BoujeeEnjinia1701/leaklisten/cad/drawings/LKL-DWG-001.pdf

CONCEPT, NOT FOR FABRICATION | LeakListen · github.com/BoujeeEnjinia1701/leaklisten

FRONT VIEW
Scale 1:10; looking at the front (along +Y)

TOP VIEW
Scale 1:10; looking down (along -Z)

RIGHT VIEW
Scale 1:10; looking at the right side (along -X)

385

600 533

STREET

180

420

480 cap top

240
SENSOR PUCK

COVER FRAME (EXISTING)

CABLE SHOWN DIRECT; 2 m FITTED

200

FLAT ANTENNA ON ITS BRACKET NECK BAR, FEET ON THE NECK WALLS

63 OD

ISOMETRIC VIEW
Not to scale; spindle cap and frame edge grey context; seen from the front right and above, about 30 deg elevation

MAIN DIMENSIONS AND INTERFACES (MM)
Logger PVC tube 63 OD x 3 wall, flanged acetal end plugs; 240 flange to flange, 283 with socket and eye bolt Sensor puck 40 x 42 aluminium on a 42 mm pot magnet (keeper plate in transport); stack 54
Seismic mass brass 20 x 20 on a 27 mm piezo disc (compression)
Spindle cap 50 square, top 480 below street (example site)
Neck bar 20 and 16 square aluminium tube, rubber feet on the neck walls; lanyard 3
Flat antenna 70 dia on a bracket on the bar, 20 gap below the 40 cover
Top plug: eye bolt, SMA bulkhead and a 3 mm status light pipe rod
Sensor cable 2 m, M12 IP68; reaches caps to about 2.2 m deep
No chamber entry; nothing touches drinking water
REV | DESCRIPTION | DATE | BY
P1 | Preliminary GA for TRL 3 (from cad/src/model.py) | 2026-09-25 | AC
P2 | 42 mm pot magnet (LKL-DDR-002) | 2026-09-25 | AC
P3 | Layout and labels tidied | 2026-09-25 | AC
P4 | Constructable design: neck bar, end plugs, chassis (LKL-DDR-003) | 2026-10-01 | AC
P5 | Status light pipe added to the top plug (decision of 2026-10-02) | 2026-10-02 | AC
LEAKLISTEN | github.com/BoujeeEnjinia1701/leaklisten

## General arrangement, logger installed

DRAWING NO.
LKL-DWG-001

REV
P5

SHEET
1 of 1

SIZE

## ANSI B

SCALE
1:10

UNITS
mm
PROJECTION | DATE
2026-10-02

DRAWN
Amish Chadha

MATERIAL / NOTES
PVC, aluminium, stainless; bought-in parts per bom/bom.csv. PRELIMINARY, NOT FOR FABRICATION
Licensed CERN-OHL-S-2.0 · Design Molecule Lab · designmolecule.com | Generated from cad/src; do not edit by hand
