BoujeeEnjinia1701/leaklisten/cad/drawings/LKL-DWG-104.pdf

BUILD PLAN SKETCH, PLAN NOT YET BUILT LeakListen · github.com/BoujeeEnjinia1701/leaklisten

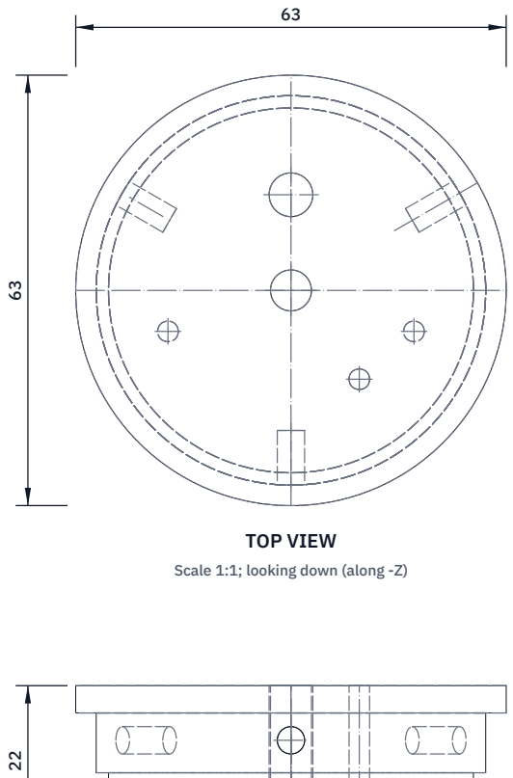
[picture p3: figure]
TOP VIEW; Scale 1:1; looking down (along -Z)

FRONT VIEW
Scale 1:1; looking at the front (along +Y)

RIGHT VIEW
Scale 1:1; looking at the right side (along -X)

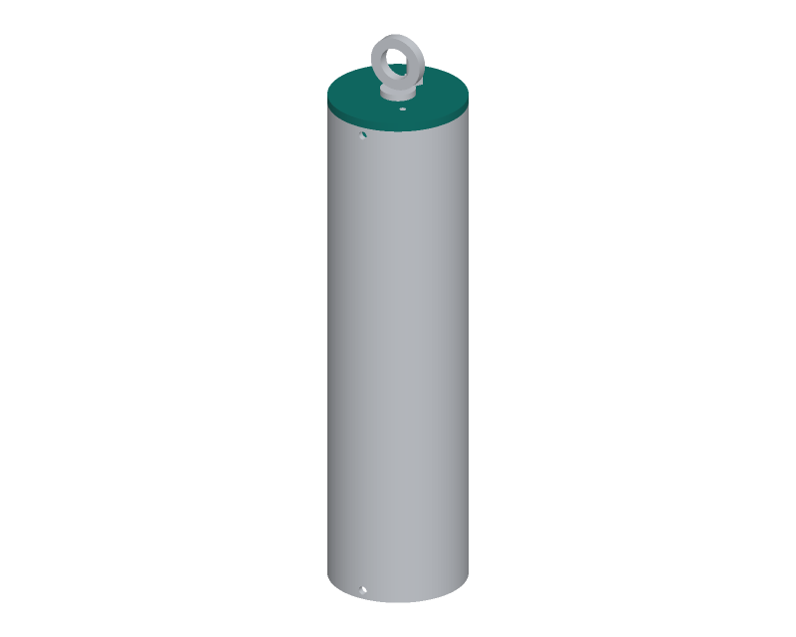
[picture p4: figure]

WHERE IT GOES
This part in colour, its neighbours in grey

HOW TO MAKE IT AND HOW IT FITS
Turn from 65 mm acetal bar: flange 63 mm diameter, 4 mm thick; spigot 57 mm diameter (a light push fit in the tube), 18 mm long.
Two O-ring grooves in the spigot, 2.5 mm wide, 1.8 mm deep, centred 10 and 15 mm below the flange, for 2.5 mm section O-rings.
Eye bolt hole 6.5 mm on the axis, right through.
SMA bulkhead hole 6.5 mm, 14 mm from the axis, right through;
check the size against the bulkhead's datasheet.
Light pipe hole 3.0 mm, right through, 13 mm from the axis on the side
away from the SMA and 10 mm toward the right-hand standoff in the top view. Inner face: two M3 tapped holes 6 mm deep for the standoffs,
18 mm each side of the axis, 6 mm toward the side away from the SMA. Radial holes: drill 3.3 mm, tap M4, through the tube's holes,
4 mm below the flange, 120 degrees apart (one away from the SMA). Check: the plug pushes in by hand with O-rings greased.
REV | DESCRIPTION | DATE | BY
P1 | Making sketch for the prototype build plan | 2026-10-01 | AC
P2 | Light pipe hole added (decision of 2026-10-02) | 2026-10-02 | AC
LEAKLISTEN | github.com/BoujeeEnjinia1701/leaklisten

## LeakListen top end plug: making sketch

DRAWING NO.
LKL-DWG-104

REV
P2

SHEET
1 of 1

SIZE

## ANSI B

SCALE
1:1

UNITS
mm
PROJECTION | DATE
2026-10-02

DRAWN
Amish Chadha

MATERIAL / NOTES
Acetal (POM) round bar, 65 mm
Licensed CERN-OHL-S-2.0 · Design Molecule Lab · designmolecule.com | Generated from cad/src; do not edit by hand
