BoujeeEnjinia1701/leaklisten/cad/drawings/LKL-DWG-101.pdf

BUILD PLAN SKETCH, PLAN NOT YET BUILT LeakListen · github.com/BoujeeEnjinia1701/leaklisten

FRONT VIEW
Scale 1:1; looking at the front (along +Y)

TOP VIEW
Scale 1:1; looking down (along -Z)

RIGHT VIEW
Scale 1:1; looking at the right side (along -X)

40

40 42

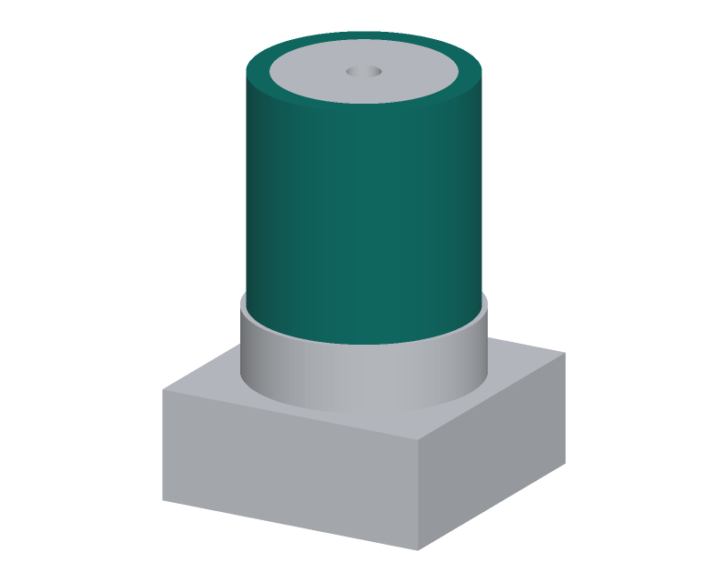
[picture p38: figure]

WHERE IT GOES
This part in colour, its neighbours in grey

HOW TO MAKE IT AND HOW IT FITS
Turn from 45 mm 6061 bar: 40 mm diameter, 42 mm long.
Base 8 mm thick. Centre drill and drill 5.0 mm, 8 mm deep, in the bottom face; tap M6, 6 mm of full thread, for the magnet's stud. Lower bore 29 mm diameter, from the top of the base up 25 mm. Upper bore 32 mm diameter, from there to the top (9 mm): the step between the bores carries the preamplifier board.
Face the base inside flat and smooth (0.8 or better): the piezo disc is bonded to it and the signal passes through it.
Break all outside edges 0.5 mm. Bead blast if you can.
Fit: magnet stud into the base with threadlocker; disc and mass on the base; board on the step; potting above the board only.
Check: the base face is flat; the M6 stud runs in by hand.
REV | DESCRIPTION | DATE | BY
P1 | Making sketch for the prototype build plan | 2026-10-01 | AC
LEAKLISTEN | github.com/BoujeeEnjinia1701/leaklisten

## LeakListen sensor puck body: making sketch

DRAWING NO.
LKL-DWG-101

REV
P1

SHEET
1 of 1

SIZE

## ANSI B

SCALE
1:1

UNITS
mm
PROJECTION | DATE
2026-10-01

DRAWN
Amish Chadha

MATERIAL / NOTES
Aluminium 6061 round bar, 45 mm
Licensed CERN-OHL-S-2.0 · Design Molecule Lab · designmolecule.com | Generated from cad/src; do not edit by hand
