BoujeeEnjinia1701/leaklisten/cad/drawings/LKL-DWG-102.pdf

BUILD PLAN SKETCH, PLAN NOT YET BUILT LeakListen · github.com/BoujeeEnjinia1701/leaklisten

FRONT VIEW
Scale 2:1; looking at the front (along +Y)

TOP VIEW
Scale 2:1; looking down (along -Z)

RIGHT VIEW
Scale 2:1; looking at the right side (along -X)

20

20 20

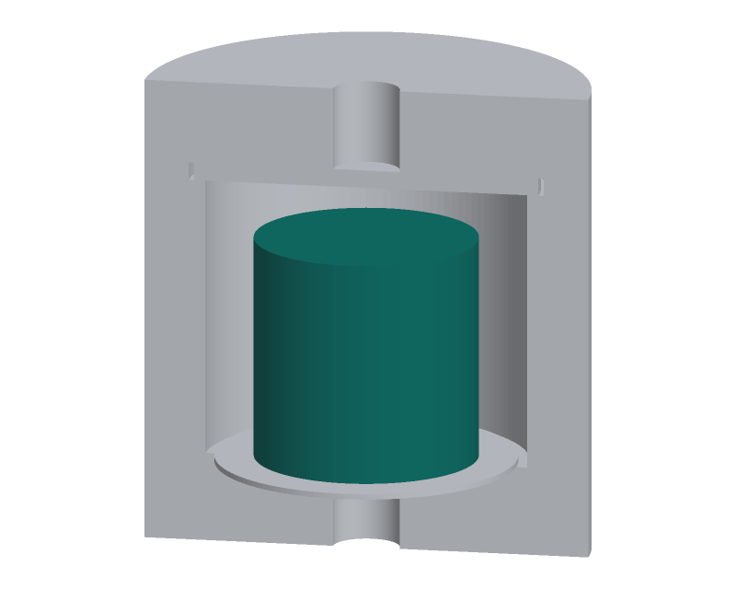
[picture p39: figure]

WHERE IT GOES
This part in colour, its neighbours in grey

HOW TO MAKE IT AND HOW IT FITS
Saw a 21 mm slice off 20 mm brass bar; face both ends to 20 mm long. The two end faces must be flat and parallel: face them in one setting each, or lap them on fine paper on glass.
Mass about 53 g; weigh it and write the figure down.
Break the edges 0.3 mm; degrease with alcohol before bonding. Fit: bonded with a thin film of rigid epoxy on the brass face of the piezo disc, centred, which is bonded to the puck base.
Nothing else touches it: 4.5 mm side gap to the bore and 4.5 mm up to the preamplifier board. No potting below the board. Check: 20 mm long, faces parallel within 0.05 mm.
REV | DESCRIPTION | DATE | BY
P1 | Making sketch for the prototype build plan | 2026-10-01 | AC
LEAKLISTEN | github.com/BoujeeEnjinia1701/leaklisten

## LeakListen seismic mass: making sketch

DRAWING NO.
LKL-DWG-102

REV
P1

SHEET
1 of 1

SIZE

## ANSI B

SCALE
2:1

UNITS
mm
PROJECTION | DATE
2026-10-01

DRAWN
Amish Chadha

MATERIAL / NOTES
Brass round bar CW614N, 20 mm
Licensed CERN-OHL-S-2.0 · Design Molecule Lab · designmolecule.com | Generated from cad/src; do not edit by hand
