BoujeeEnjinia1701/leaklisten/cad/drawings/LKL-DWG-103.pdf

BUILD PLAN SKETCH, PLAN NOT YET BUILT LeakListen · github.com/BoujeeEnjinia1701/leaklisten

FRONT VIEW
Scale 1:5; looking at the front (along +Y)

TOP VIEW
Scale 1:5; looking down (along -Z)

RIGHT VIEW
Scale 1:5; looking at the right side (along -X)

63

63 232

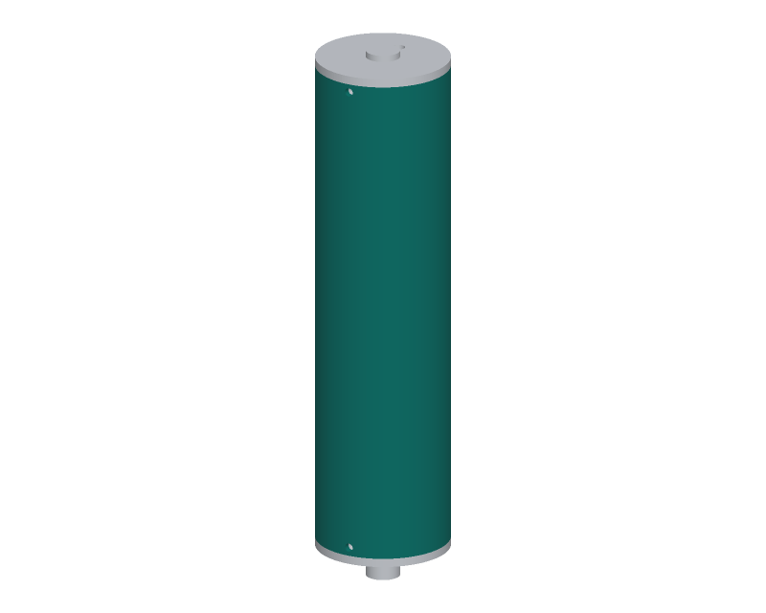
[picture p40: figure]

WHERE IT GOES
This part in colour, its neighbours in grey

HOW TO MAKE IT AND HOW IT FITS
Cut 232 mm off 63 x 3 mm PVC pressure pipe with a fine saw in a mitre box; square the ends by sanding on a flat board.
Chamfer the inside of both ends 1 mm x 30 degrees so the O-rings slide in without cutting. Deburr inside and out.
Six 4.5 mm screw holes, 4 mm from each end: three at each end, 120 degrees apart. Mark them with a paper wrap round the tube. Drill the holes with the plug fitted, so the plug can be drilled
3.3 mm and tapped M4 through the same holes (see the plugs). Fit: plug spigots slide in until the flanges sit on the tube ends; both O-rings on each plug are inside, beyond the screws. Check: the ends are square; no scratches along the bore
in the 25 mm at each end where the O-rings seal.
REV | DESCRIPTION | DATE | BY
P1 | Making sketch for the prototype build plan | 2026-10-01 | AC
LEAKLISTEN | github.com/BoujeeEnjinia1701/leaklisten

## LeakListen logger tube: making sketch

DRAWING NO.
LKL-DWG-103

REV
P1

SHEET
1 of 1

SIZE

## ANSI B

SCALE
1:5

UNITS
mm
PROJECTION | DATE
2026-10-01

DRAWN
Amish Chadha

MATERIAL / NOTES
PVC pressure pipe 63 mm OD, 3 mm wall
Licensed CERN-OHL-S-2.0 · Design Molecule Lab · designmolecule.com | Generated from cad/src; do not edit by hand
