BoujeeEnjinia1701/leaklisten/cad/drawings/LKL-DWG-105.pdf

BUILD PLAN SKETCH, PLAN NOT YET BUILT LeakListen · github.com/BoujeeEnjinia1701/leaklisten

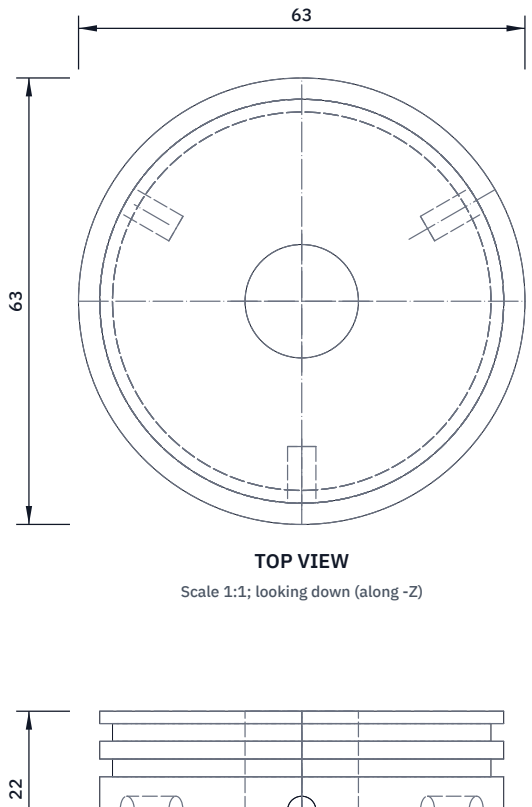
[picture p41: figure]
TOP VIEW; Scale 1:1; looking down (along -Z)

FRONT VIEW
Scale 1:1; looking at the front (along +Y)

RIGHT VIEW
Scale 1:1; looking at the right side (along -X)

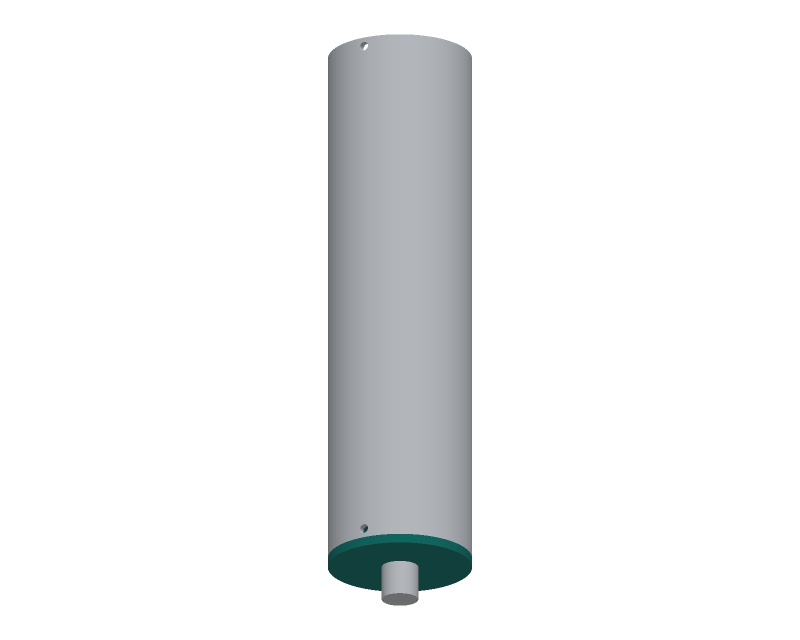
[picture p42: figure]

WHERE IT GOES
This part in colour, its neighbours in grey

HOW TO MAKE IT AND HOW IT FITS
Turn as the top plug: flange 63 mm x 4 mm, spigot 57 mm x 18 mm, two O-ring grooves 2.5 x 1.8 mm, 10 and 15 mm above the flange. Centre hole: drill 14.5 mm and tap M16 x 1.5 right through, for
the front-mount M12 panel socket (check its thread first).
Face the outside of the flange flat where the socket's O-ring sits. Radial holes: drill 3.3 mm, tap M4, through the tube's holes,
4 mm above the flange, 120 degrees apart.
Fit: the socket screws in from outside with its O-ring under its flange; its lock nut and the board lead are inside.
Check: the socket seats flat; the plug pushes in by hand.
REV | DESCRIPTION | DATE | BY
P1 | Making sketch for the prototype build plan | 2026-10-01 | AC
LEAKLISTEN | github.com/BoujeeEnjinia1701/leaklisten

## LeakListen bottom end plug: making sketch

DRAWING NO.
LKL-DWG-105

REV
P1

SHEET
1 of 1

SIZE

## ANSI B

SCALE
1:1

UNITS
mm
PROJECTION | DATE
2026-10-01

DRAWN
Amish Chadha

MATERIAL / NOTES
Acetal (POM) round bar, 65 mm
Licensed CERN-OHL-S-2.0 · Design Molecule Lab · designmolecule.com | Generated from cad/src; do not edit by hand
