BoujeeEnjinia1701/leaklisten/cad/drawings/LKL-DWG-106.pdf

BUILD PLAN SKETCH, PLAN NOT YET BUILT LeakListen · github.com/BoujeeEnjinia1701/leaklisten

FRONT VIEW
Scale 1:2; looking at the front (along +Y)

TOP VIEW
Scale 1:2; looking down (along -Z)

RIGHT VIEW
Scale 1:2; looking at the right side (along -X)

48

26 158

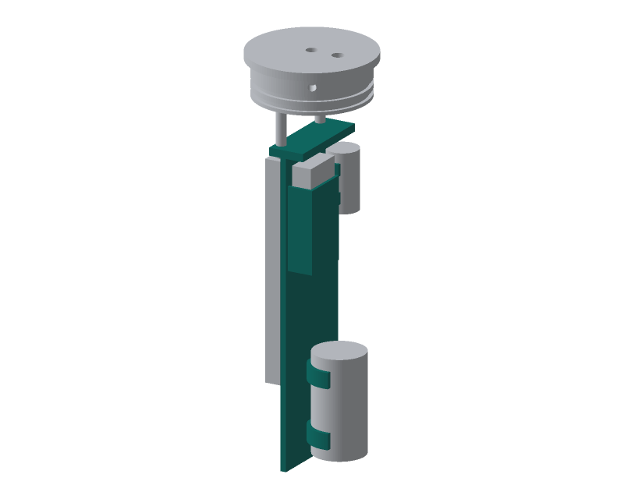
[picture p43: figure]

WHERE IT GOES
This part in colour, its neighbours in grey

HOW TO MAKE IT AND HOW IT FITS
Print lying on its board face, with support under the 6 mm of the top tab that stands out on that side. Spine 48 x 3 x 158 mm.
Top tab 48 x 18 x 4 mm across the top of the spine, with two 3.2 mm holes 18 mm each side of centre, 6 mm out on the board side:
M3 screws up through these (before the board goes on) into
the two M3 x 20 standoffs that hang it from the top plug.
Clip face (dashed in the front view), from the top: two clips for
the 16 mm capacitor, 8 and 30 mm down; a 22 x 10 x 50 mm pocket for the desiccant,
open at the top; at the bottom, two clips for the C cell, 10 and
40 mm up from the bottom edge. Clips wrap about 200 degrees. Board face: four 2.5 mm pilot holes for the board standoffs,
30 mm apart across and 100 mm apart down.
Fit: the cell and capacitor snap into their clips.
Check: it slides into the tube with 2.5 mm to spare all round.
REV | DESCRIPTION | DATE | BY
P1 | Making sketch for the prototype build plan | 2026-10-01 | AC
LEAKLISTEN | github.com/BoujeeEnjinia1701/leaklisten

## LeakListen internal chassis: making sketch

DRAWING NO.
LKL-DWG-106

REV
P1

SHEET
1 of 1

SIZE

## ANSI B

SCALE
1:2

UNITS
mm
PROJECTION | DATE
2026-10-01

DRAWN
Amish Chadha

MATERIAL / NOTES
PETG, 3D printed, 40 % infill
Licensed CERN-OHL-S-2.0 · Design Molecule Lab · designmolecule.com | Generated from cad/src; do not edit by hand
