BoujeeEnjinia1701/leaklisten/cad/drawings/LKL-DWG-107.pdf

BUILD PLAN SKETCH, PLAN NOT YET BUILT LeakListen · github.com/BoujeeEnjinia1701/leaklisten

FRONT VIEW
Scale 1:2; looking at the front (along +Y)

TOP VIEW
Scale 1:2; looking down (along -Z)

RIGHT VIEW
Scale 1:2; looking at the right side (along -X)

350

20 20

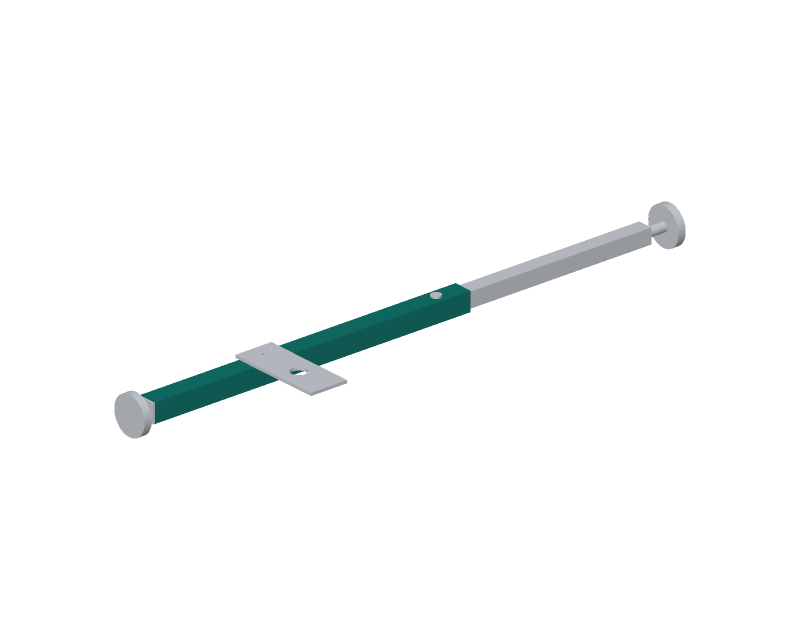
[picture p44: figure]

WHERE IT GOES
This part in colour, its neighbours in grey

HOW TO MAKE IT AND HOW IT FITS
Cut 350 mm of 20 x 20 x 1.5 mm square tube; square and deburr. Measure from the foot end (the end that takes the fixed foot): bracket bolt hole 5.5 mm at 130 mm, top and bottom walls; locking pin hole 6.5 mm at 320 mm, top and bottom walls. Drill each pair straight through both walls in a drill stand so the holes line up.
Press a 20 x 20 tube insert with an M10 nut into the foot end. Fit: the inner tube slides into the other end with 0.5 mm clearance; the pin goes through both tubes.
Check: the inner tube slides the full length without binding.
REV | DESCRIPTION | DATE | BY
P1 | Making sketch for the prototype build plan | 2026-10-01 | AC
LEAKLISTEN | github.com/BoujeeEnjinia1701/leaklisten

## LeakListen neck bar outer tube: making sketch

DRAWING NO.
LKL-DWG-107

REV
P1

SHEET
1 of 1

SIZE

## ANSI B

SCALE
1:2

UNITS
mm
PROJECTION | DATE
2026-10-01

DRAWN
Amish Chadha

MATERIAL / NOTES
Aluminium square tube 20 x 20 x 1.5 mm, 6063
Licensed CERN-OHL-S-2.0 · Design Molecule Lab · designmolecule.com | Generated from cad/src; do not edit by hand
