BoujeeEnjinia1701/leaklisten/cad/drawings/LKL-DWG-108.pdf

BUILD PLAN SKETCH, PLAN NOT YET BUILT LeakListen · github.com/BoujeeEnjinia1701/leaklisten

FRONT VIEW
Scale 1:2; looking at the front (along +Y)

TOP VIEW
Scale 1:2; looking down (along -Z)

RIGHT VIEW
Scale 1:2; looking at the right side (along -X)

350

16 16

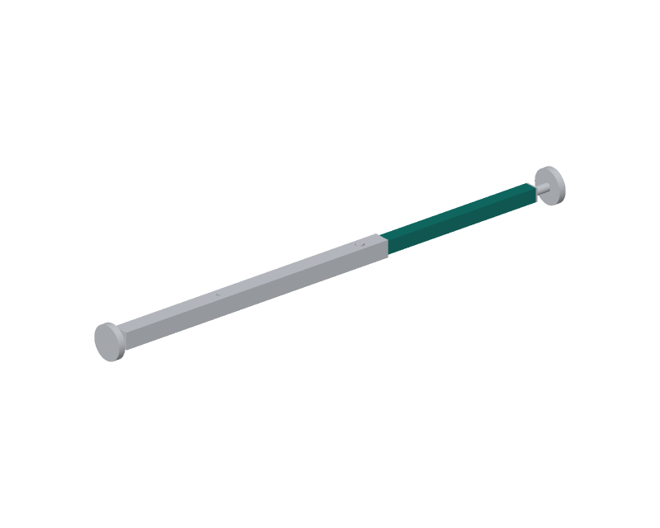
[picture p45: figure]

WHERE IT GOES
This part in colour, its neighbours in grey

HOW TO MAKE IT AND HOW IT FITS
Cut 350 mm of 16 x 16 x 1.5 mm square tube; square and deburr. Seven locking pin holes, 6.5 mm, through the top and bottom walls, 20 mm apart, the first 20 mm from the plain end (20 to 140 mm). Press a 16 x 16 tube insert with an M10 nut into the far end.
Fit: slide into the outer tube; choose the hole that sets the bar about 20 mm short of the neck width, fit the pin and R-clip, then wind the feet out to take up the last 20 mm.
With the 7 holes and about 30 mm of foot travel the bar spans necks of about 570 to 710 mm (600 mm as drawn, hole 6 of 7). Check: the pin drops through both tubes at every hole.
REV | DESCRIPTION | DATE | BY
P1 | Making sketch for the prototype build plan | 2026-10-01 | AC
LEAKLISTEN | github.com/BoujeeEnjinia1701/leaklisten

## LeakListen neck bar inner tube: making sketch

DRAWING NO.
LKL-DWG-108

REV
P1

SHEET
1 of 1

SIZE

## ANSI B

SCALE
1:2

UNITS
mm
PROJECTION | DATE
2026-10-01

DRAWN
Amish Chadha

MATERIAL / NOTES
Aluminium square tube 16 x 16 x 1.5 mm, 6063
Licensed CERN-OHL-S-2.0 · Design Molecule Lab · designmolecule.com | Generated from cad/src; do not edit by hand
