BoujeeEnjinia1701/leaklisten/cad/drawings/LKL-DWG-109.pdf

BUILD PLAN SKETCH, PLAN NOT YET BUILT LeakListen · github.com/BoujeeEnjinia1701/leaklisten

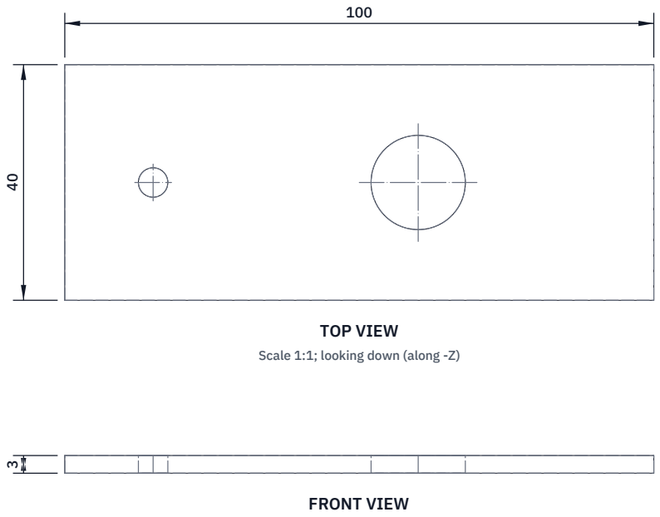
[picture p46: figure]
FRONT VIEW; TOP VIEW; Scale 1:1; looking down (along -Z)

Scale 1:1; looking at the front (along +Y)

RIGHT VIEW
Scale 1:1; looking at the right side (along -X)

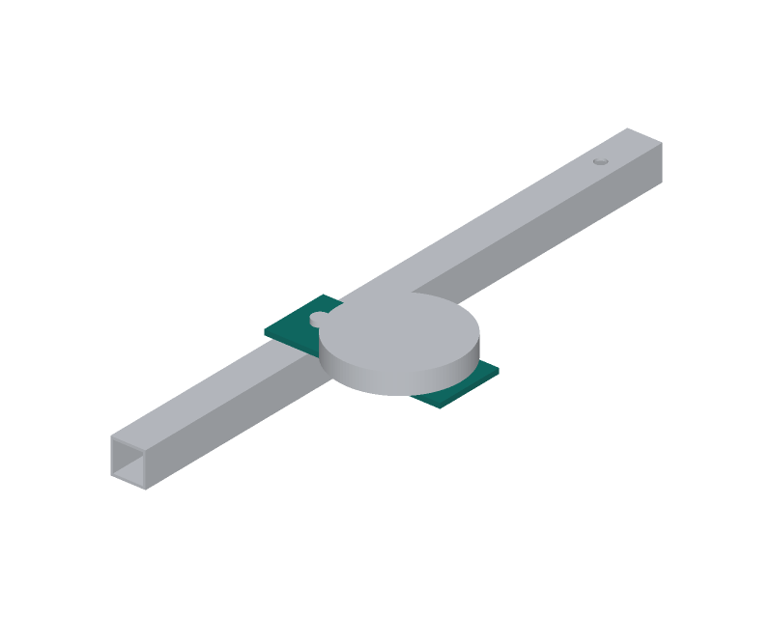
[picture p47: figure]

WHERE IT GOES
This part in colour, its neighbours in grey

HOW TO MAKE IT AND HOW IT FITS
Cut 100 mm of 40 x 3 mm flat bar; round the corners 3 mm, deburr. On the centre line: bolt hole 5.5 mm, 15 mm from one end;
antenna stud hole 60 mm from the same end, sized to the antenna's stud (16.5 mm for an M16 stud; check its datasheet).
Fit: the bracket lies flat across the top of the outer tube, the
bolt hole over the tube; one M5 x 30 bolt through bracket and tube, nyloc nut under the tube.
The antenna sits on top, its stud through the large hole, nut underneath; the antenna is 45 mm off the bar's centre line. Check: the antenna sits flat and the bracket cannot turn when the bolt is tight (bracket edge against your thumb).
REV | DESCRIPTION | DATE | BY
P1 | Making sketch for the prototype build plan | 2026-10-01 | AC
LEAKLISTEN | github.com/BoujeeEnjinia1701/leaklisten

## LeakListen antenna bracket: making sketch

DRAWING NO.
LKL-DWG-109

REV
P1

SHEET
1 of 1

SIZE

## ANSI B

SCALE
1:1

UNITS
mm
PROJECTION | DATE
2026-10-01

DRAWN
Amish Chadha

MATERIAL / NOTES
Aluminium flat bar 40 x 3 mm, 6082
Licensed CERN-OHL-S-2.0 · Design Molecule Lab · designmolecule.com | Generated from cad/src; do not edit by hand
