BoujeeEnjinia1701/leaklisten/cad/drawings/LKL-DWG-001.png

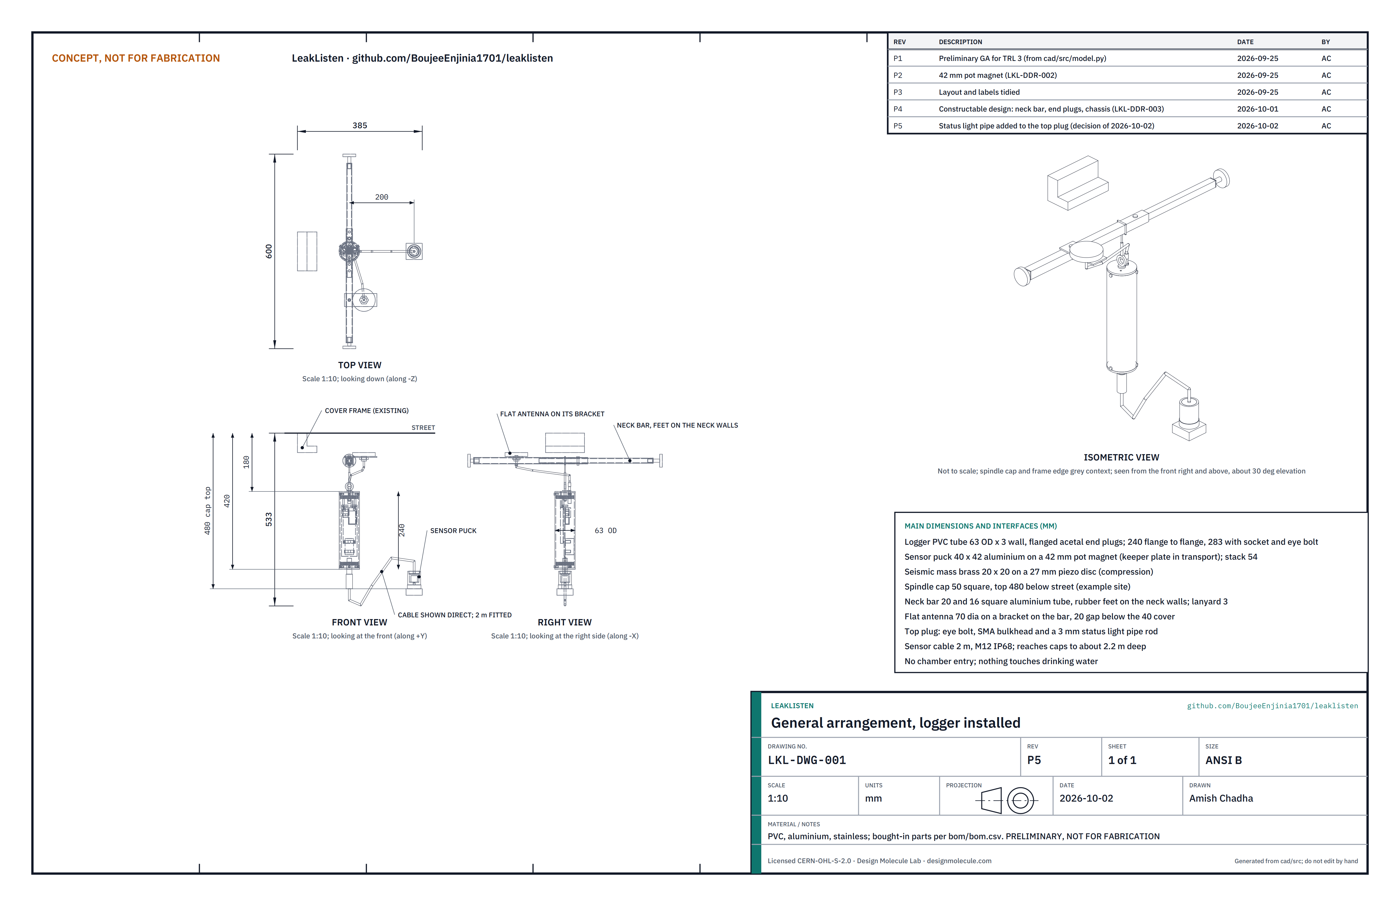
cad/drawings/LKL-DWG-001.png
