BoujeeEnjinia1701/leaklisten/media/card.png

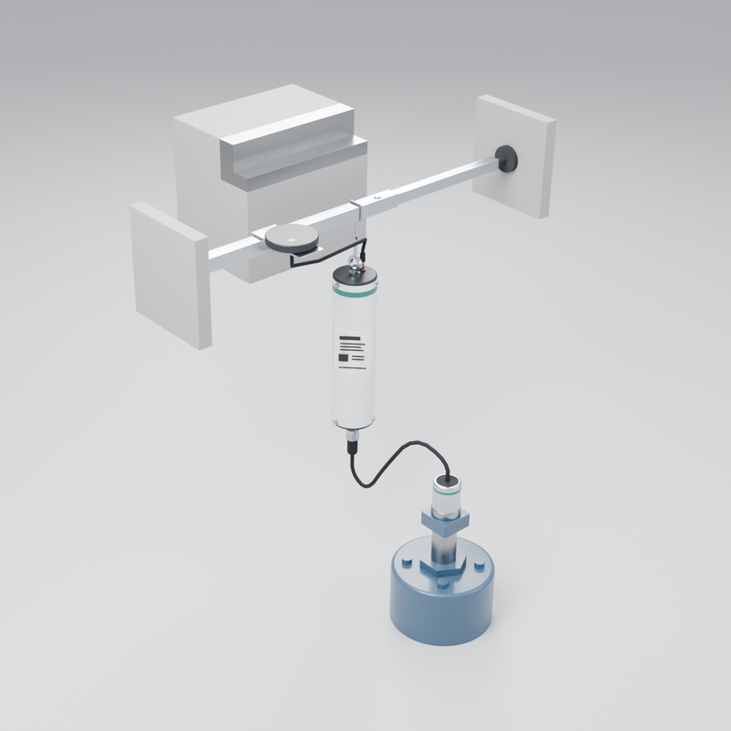
media/card.png
