BoujeeEnjinia1701/leaklisten/media/cutaway.png

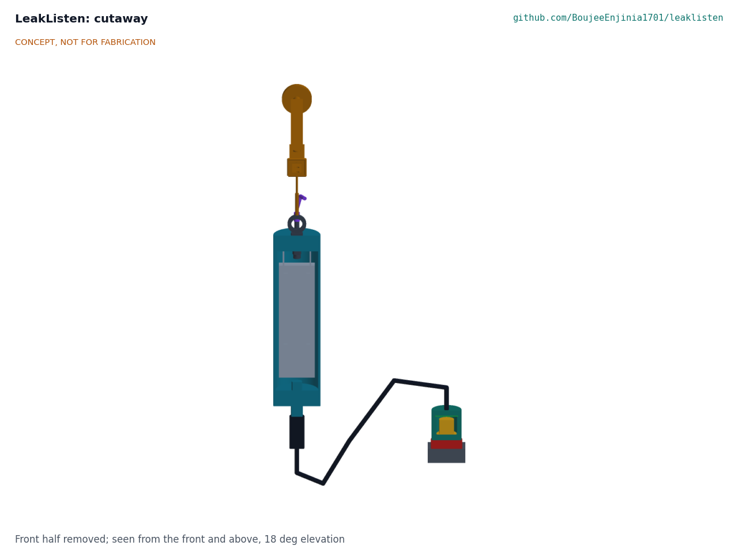
media/cutaway.png
