BoujeeEnjinia1701/leaklisten/media/exploded.png

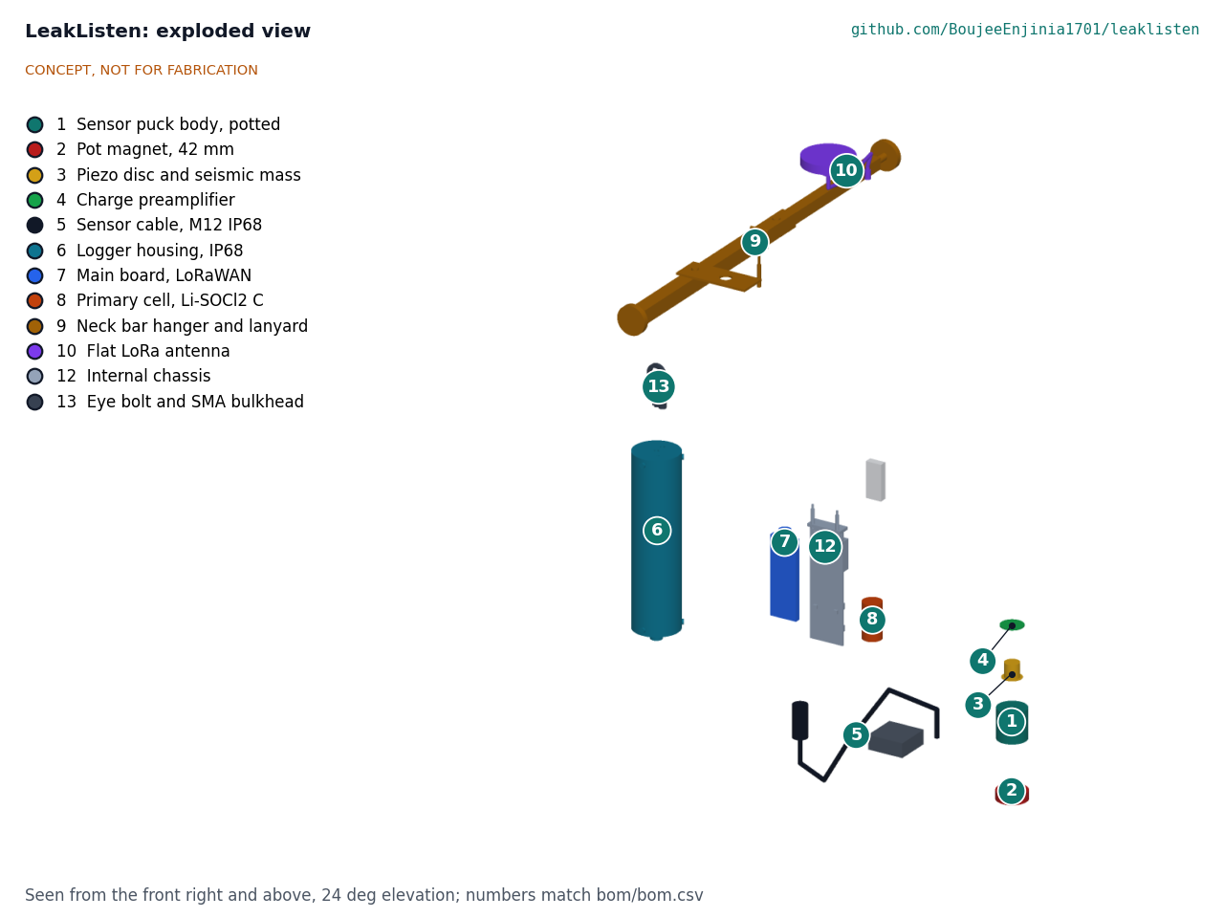
media/exploded.png
