BoujeeEnjinia1701/leaklisten/media/flow.png

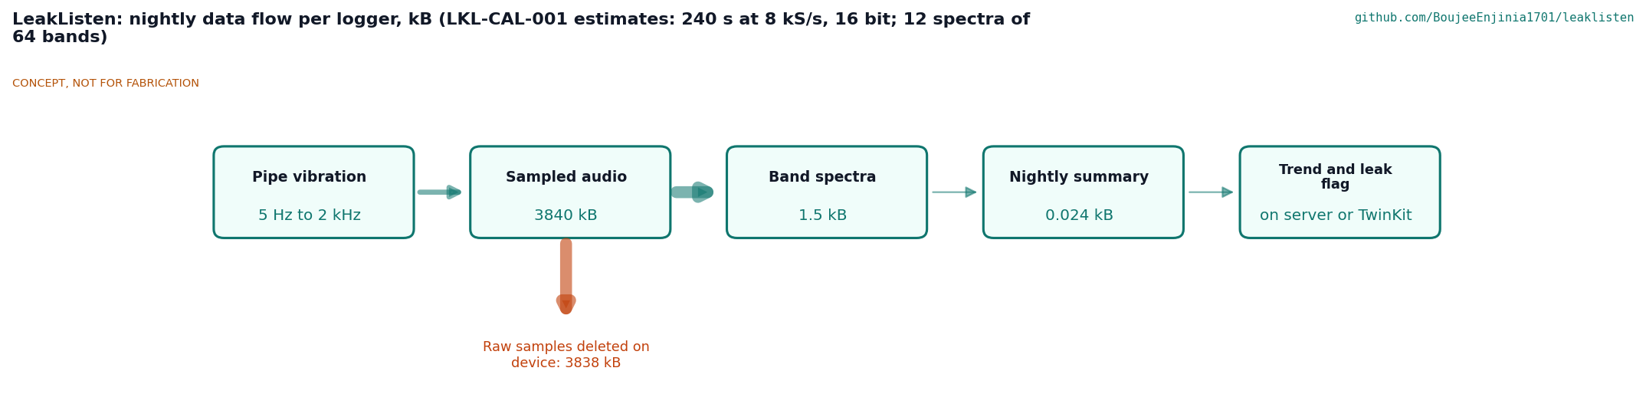
media/flow.png
