BoujeeEnjinia1701/leaklisten/media/hero.png

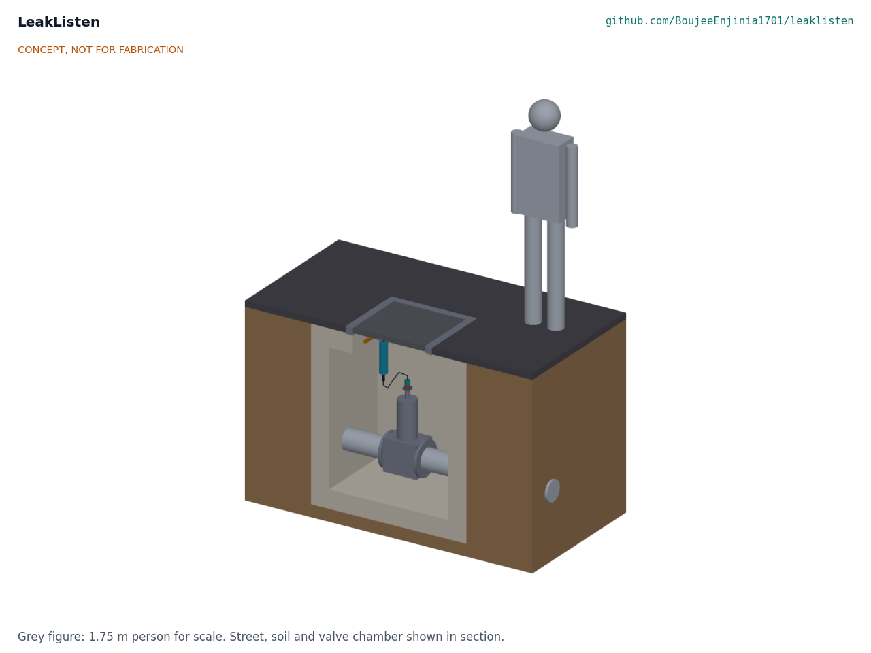
media/hero.png
