BoujeeEnjinia1701/leaklisten/media/render-detail.png

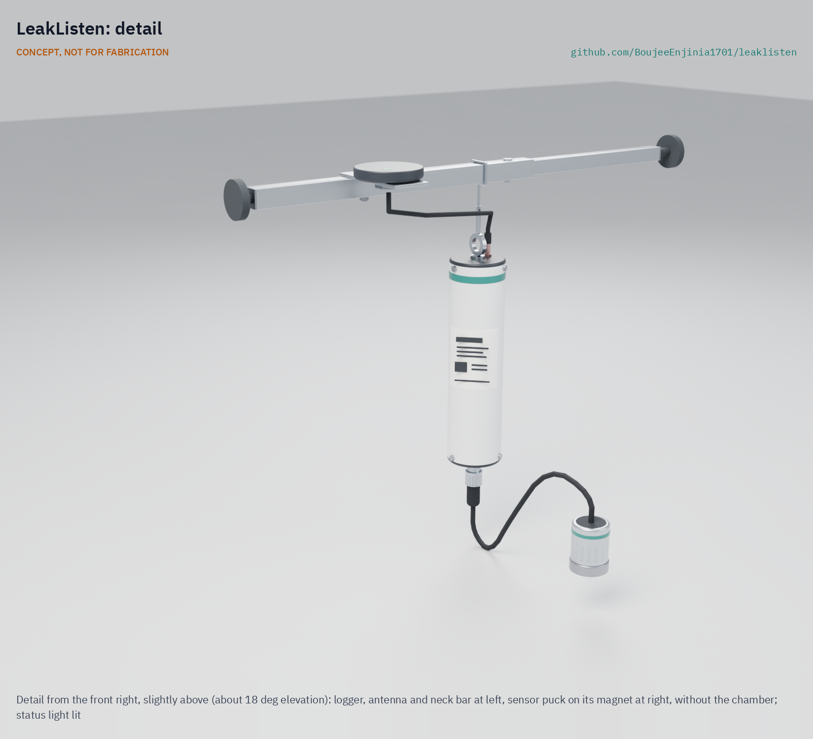
media/render-detail.png
