BoujeeEnjinia1701/leaklisten/media/render-exploded.png

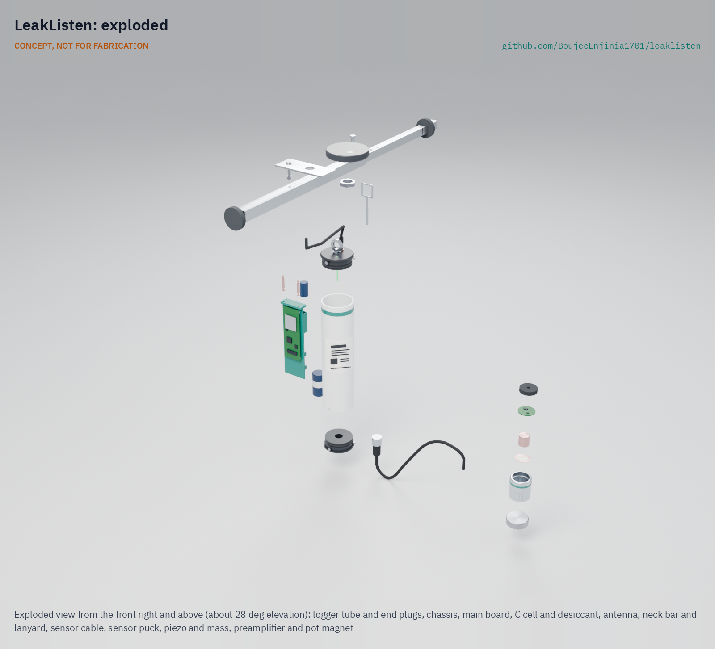
media/render-exploded.png
