BoujeeEnjinia1701/leaklisten/media/social-preview.png

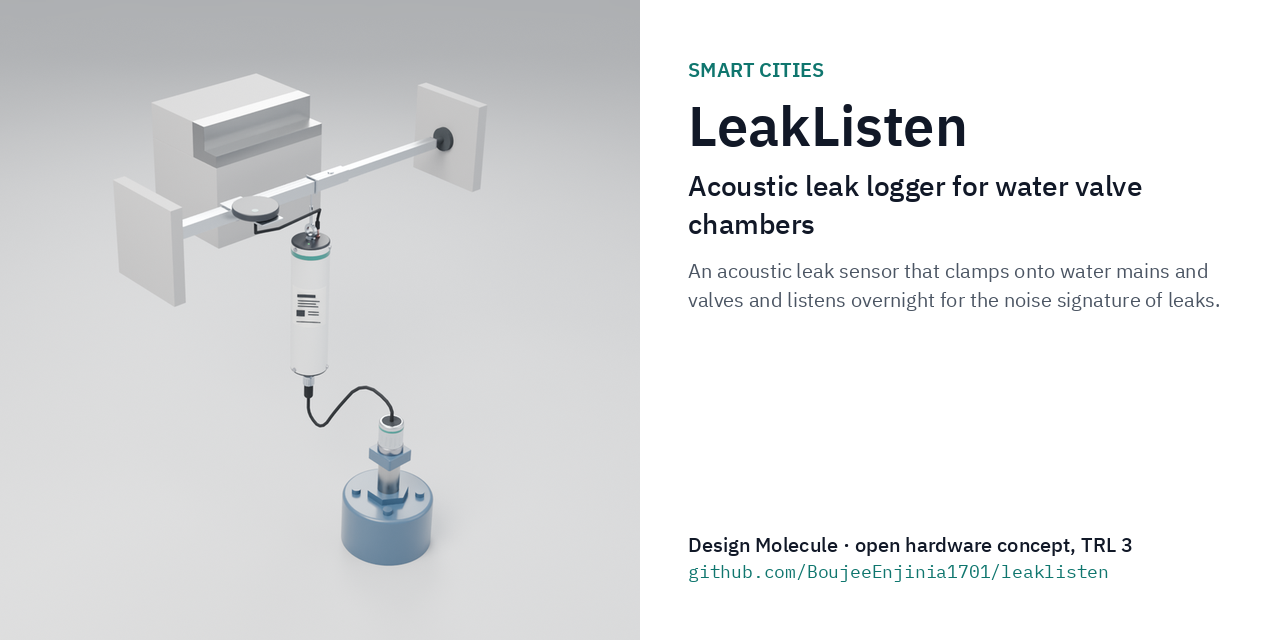
media/social-preview.png
